uwasystemhealth/VM3000-Microphones/Images/16-GB-MicroSD.PNG

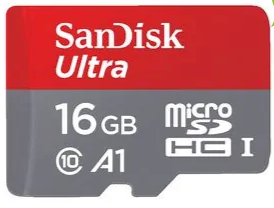
Images/16-GB-MicroSD.PNG
