uwasystemhealth/VM3000-Microphones/Images/05112020_PDM_Stereo.PNG

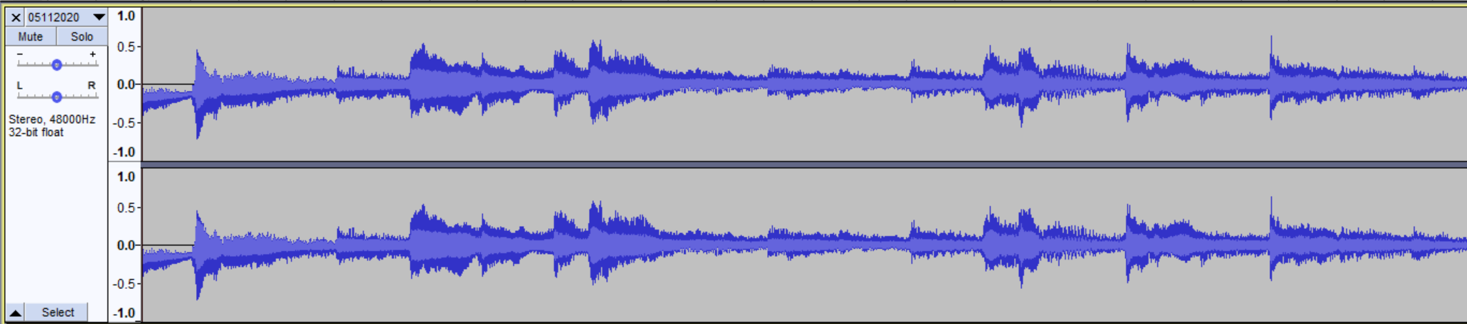
Images/05112020_PDM_Stereo.PNG
