uwasystemhealth/VM3000-Microphones/Images/I2S-MEMS-Breakout.jpg

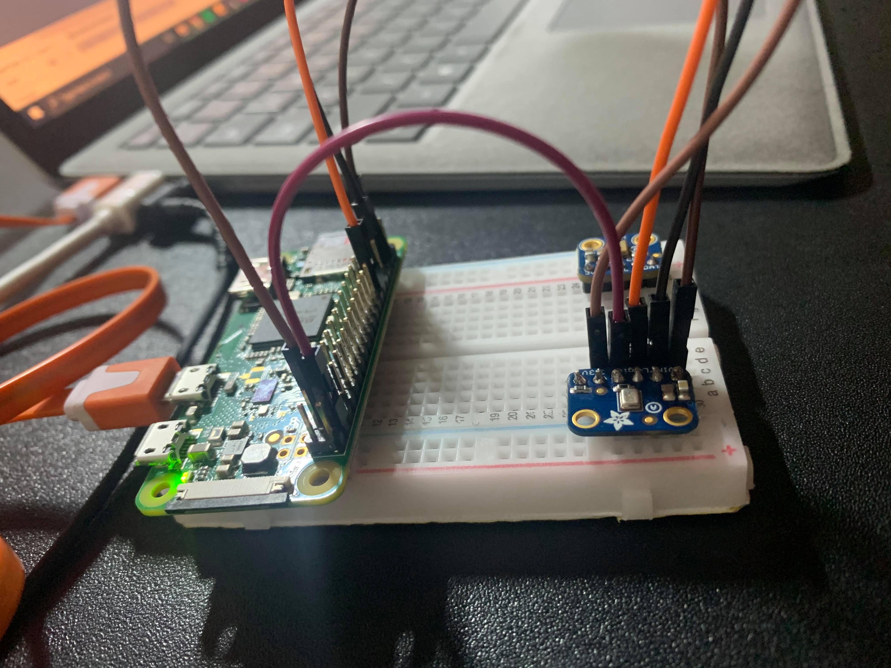
Images/I2S-MEMS-Breakout.jpg
