uwasystemhealth/VM3000-Microphones/Images/No_Phantom_Noise_Labelled_axes_legend_fixed.png

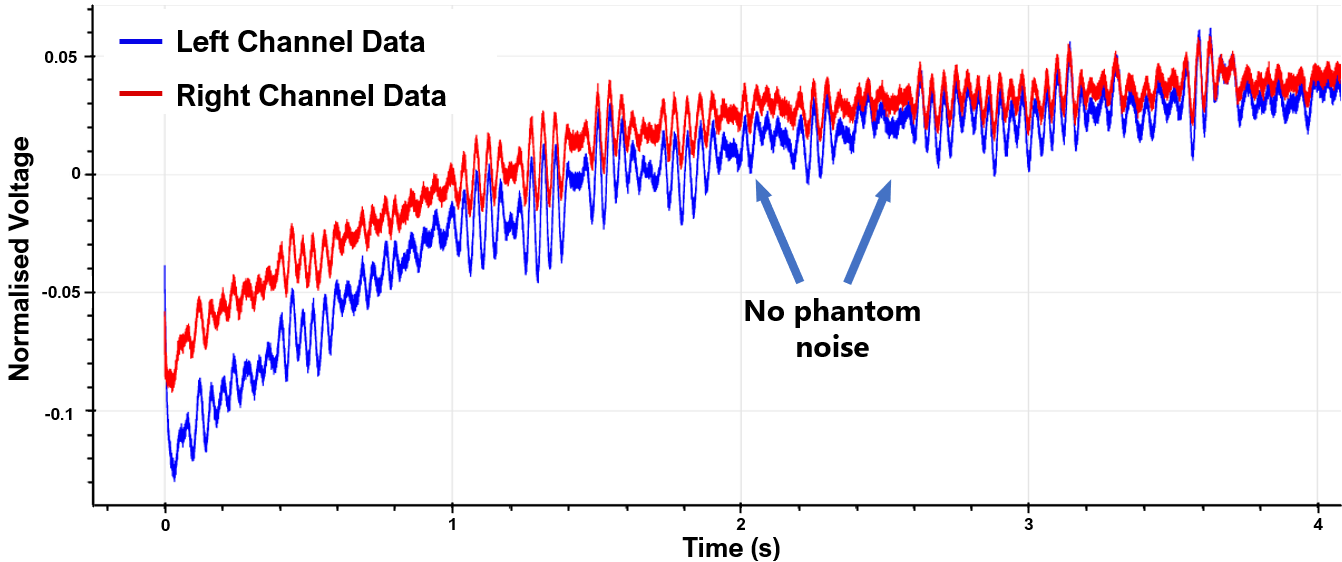
Images/No_Phantom_Noise_Labelled_axes_legend_fixed.png
