uwasystemhealth/VM3000-Microphones/Images/PDM-MEMS-Breakout.jpg

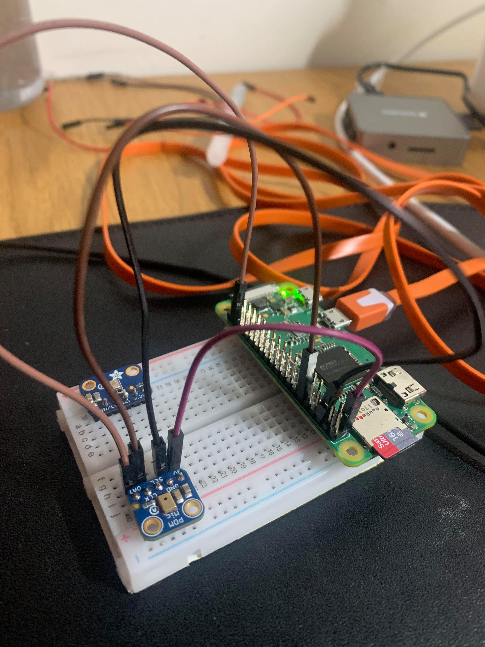
Images/PDM-MEMS-Breakout.jpg
