uwasystemhealth/VM3000-Microphones/Images/PDM_Microphone_Array_Prototype_Board.PNG

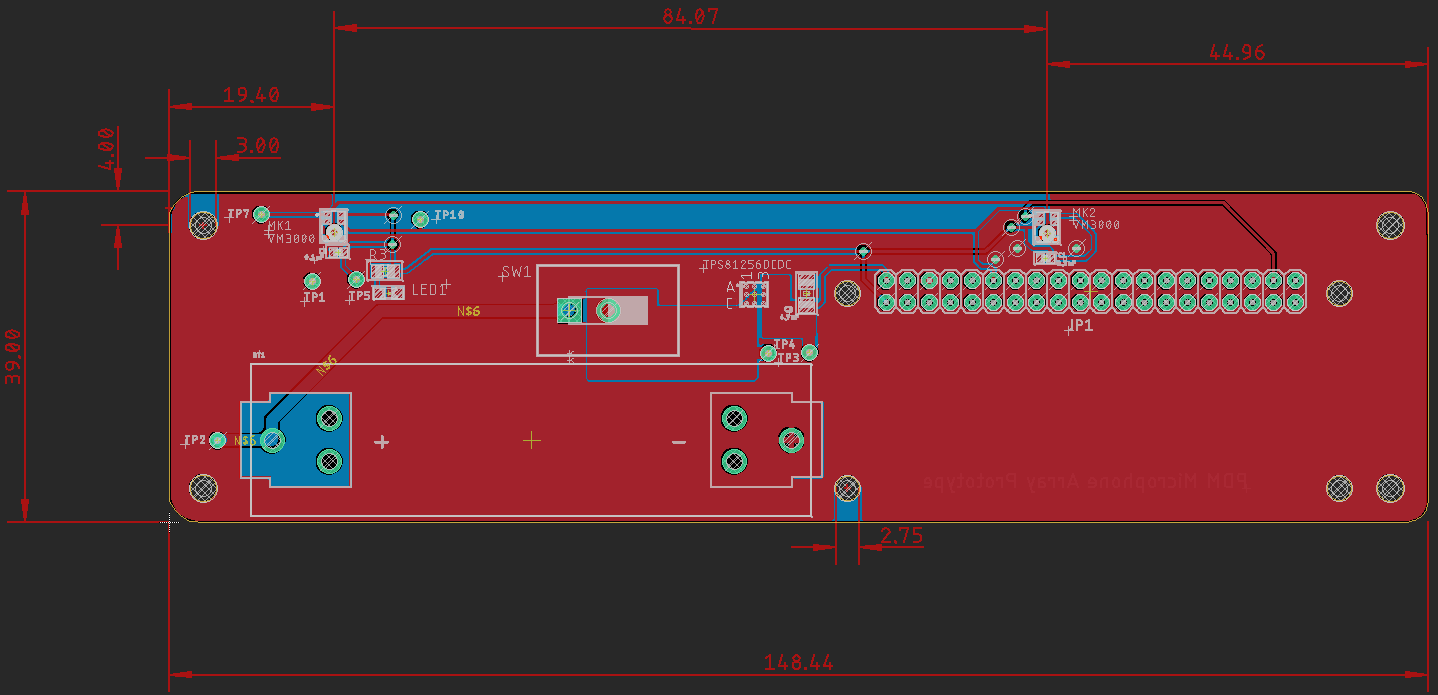
Images/PDM_Microphone_Array_Prototype_Board.PNG
