uwasystemhealth/VM3000-Microphones/Images/Phantom_Noise_1_labelled_axes_legend_fixed.png

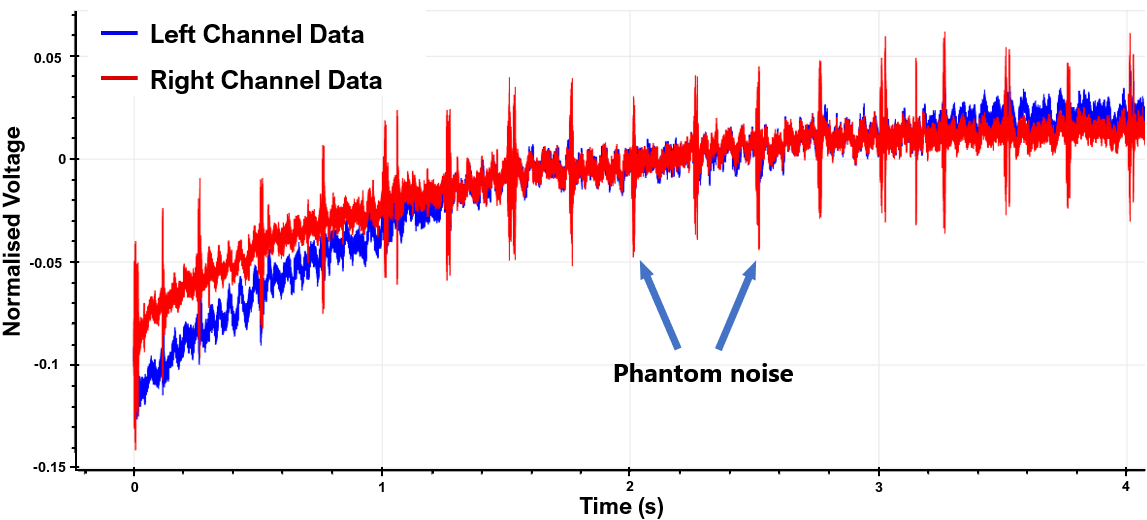
Images/Phantom_Noise_1_labelled_axes_legend_fixed.png
