uwasystemhealth/VM3000-Microphones/Images/Pi-Zero-W-GPIO.PNG

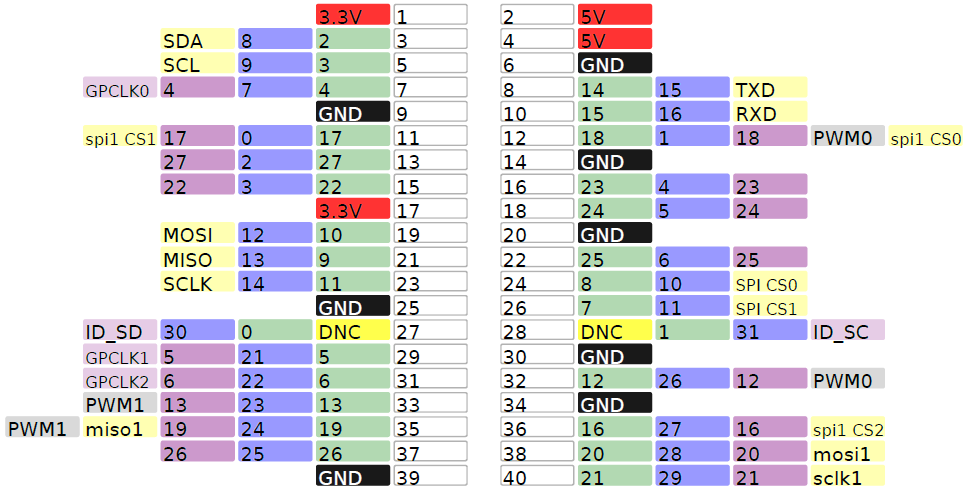
Images/Pi-Zero-W-GPIO.PNG
