uwasystemhealth/VM3000-Microphones/Images/Populated_Prototype_1.jpg

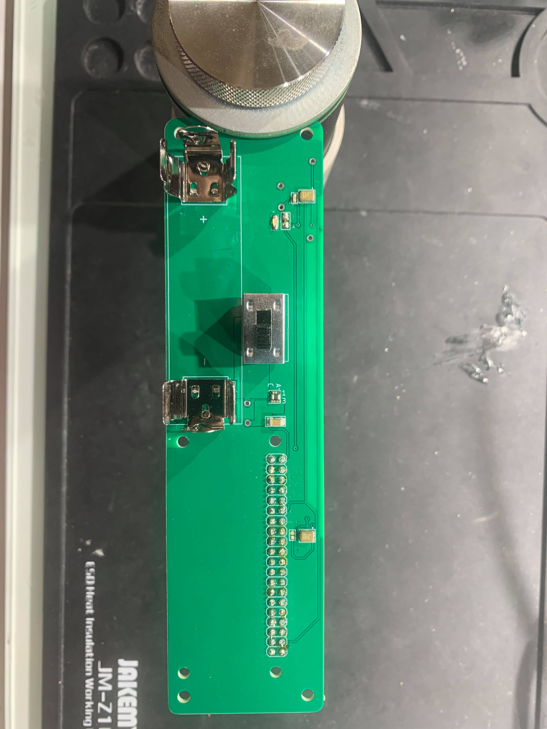
Images/Populated_Prototype_1.jpg
