uwasystemhealth/VM3000-Microphones/Images/Populated_Prototype_2.jpg

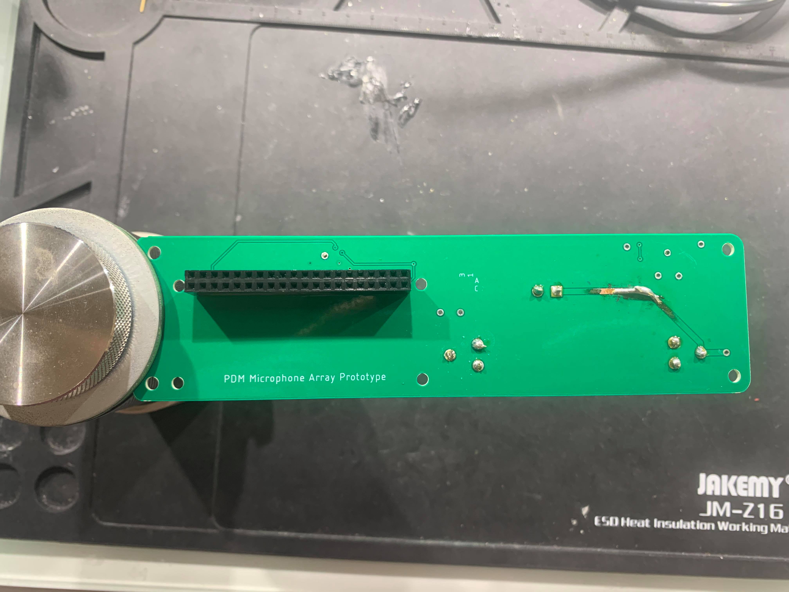
Images/Populated_Prototype_2.jpg
