uwasystemhealth/VM3000-Microphones/Images/Populated_Prototype_3.jpg

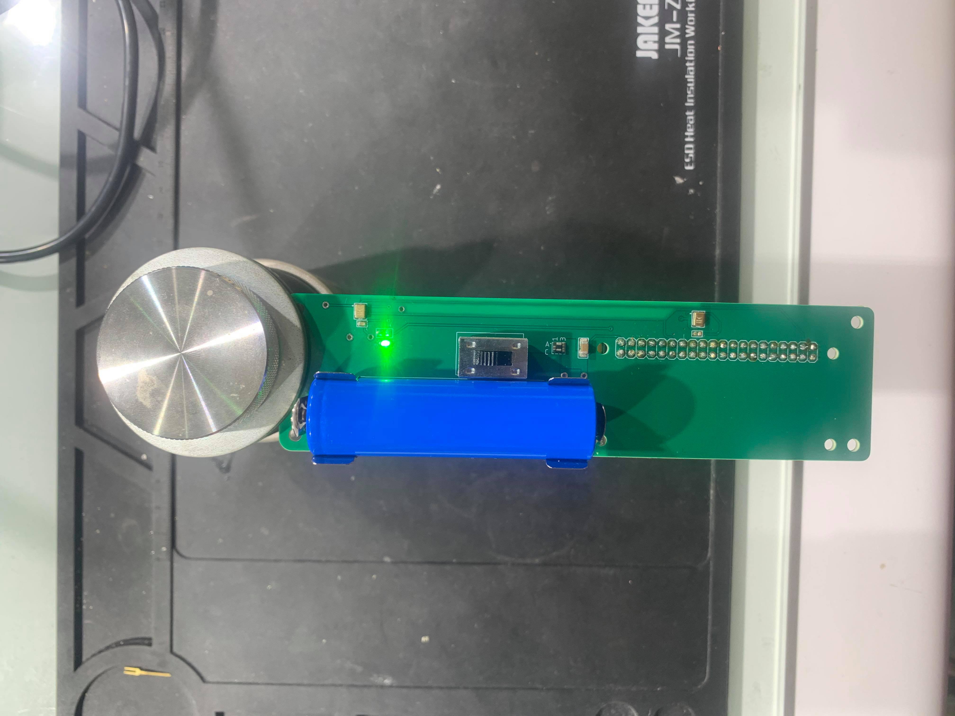
Images/Populated_Prototype_3.jpg
