uwasystemhealth/VM3000-Microphones/Images/Populated_Prototype_4.jpg

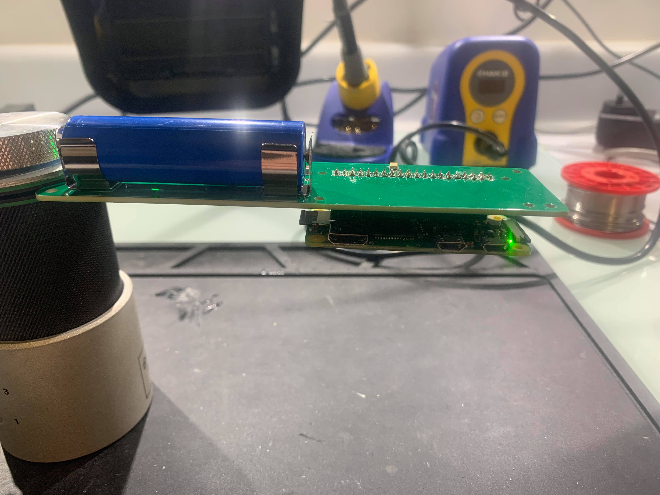
Images/Populated_Prototype_4.jpg
