uwasystemhealth/VM3000-Microphones/Images/Populated_Prototype_5.jpg

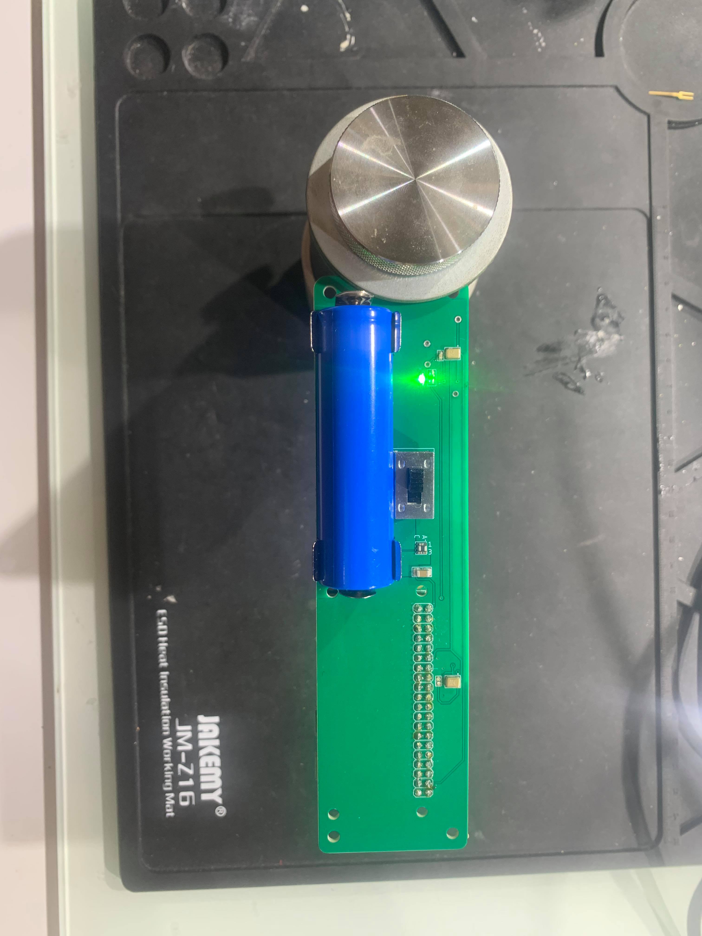
Images/Populated_Prototype_5.jpg
