uwasystemhealth/VM3000-Microphones/Images/Pulse-Density-Modulation-Example.png

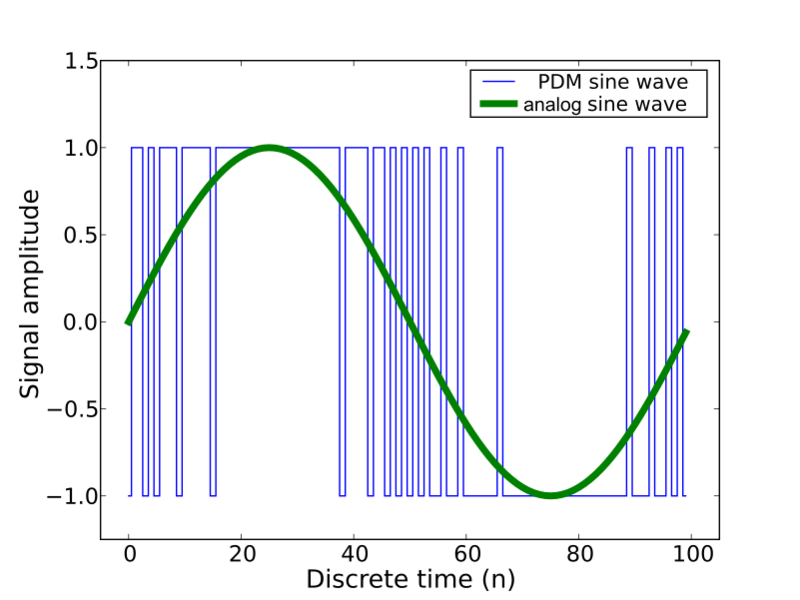
Images/Pulse-Density-Modulation-Example.png
