uwasystemhealth/VM3000-Microphones/Images/Sound-Circuit.jpg

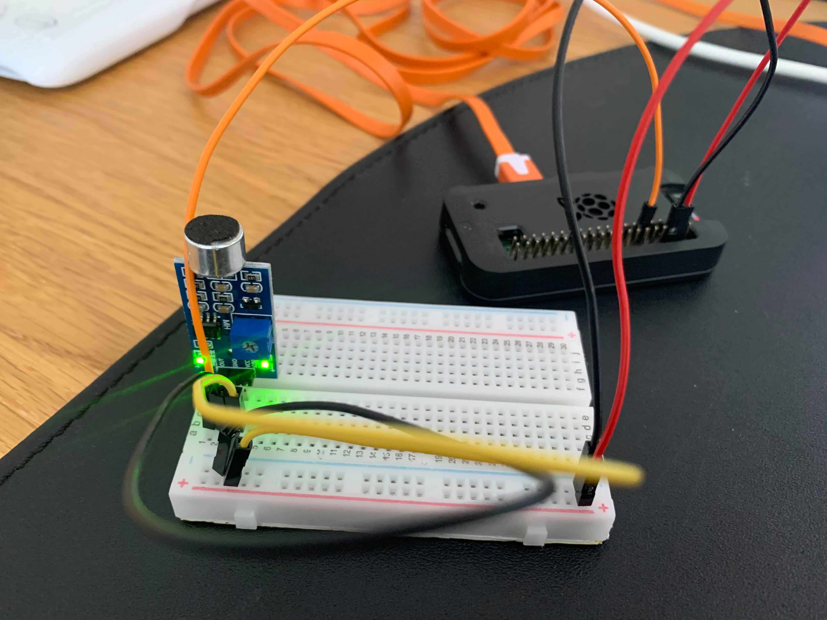
Images/Sound-Circuit.jpg
