uwasystemhealth/VM3000-Microphones/Images/Verbatim-Multi-Card-Reader.PNG

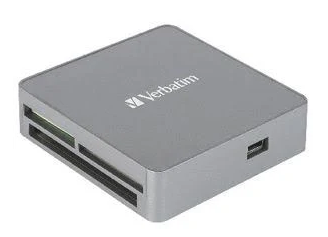
Images/Verbatim-Multi-Card-Reader.PNG
