uwasystemhealth/VM3000-Microphones/Images/WinSCP.PNG

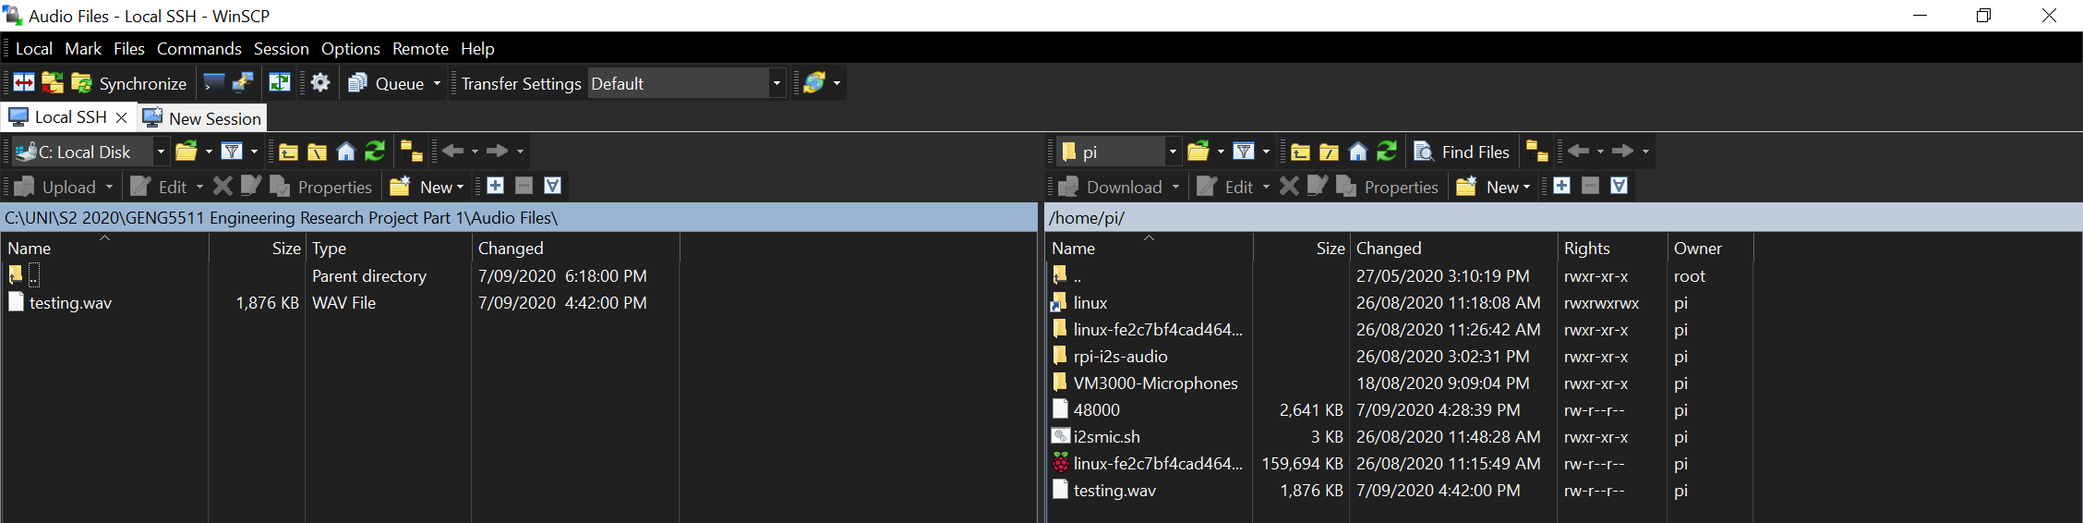
Images/WinSCP.PNG
