uwasystemhealth/VM3000-Microphones/Images/Anechoic_Setup_1.jpg

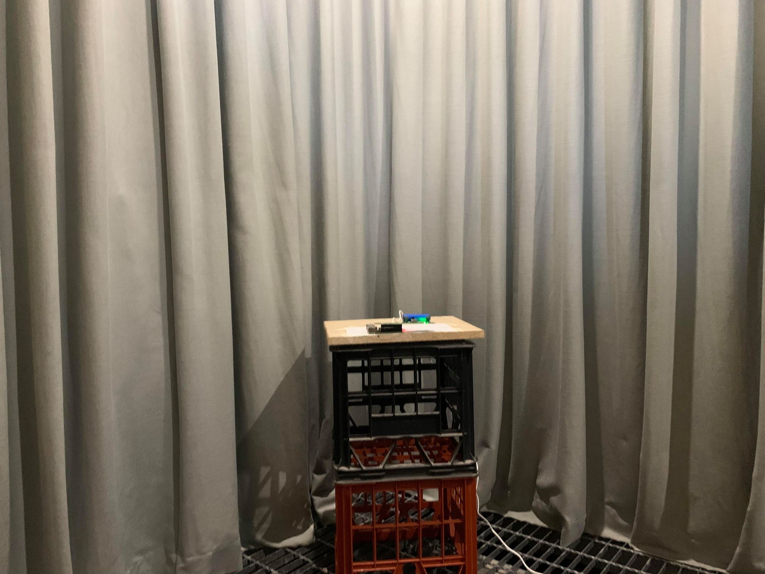
Images/Anechoic_Setup_1.jpg
