uwasystemhealth/VM3000-Microphones/Images/Setup_3.png

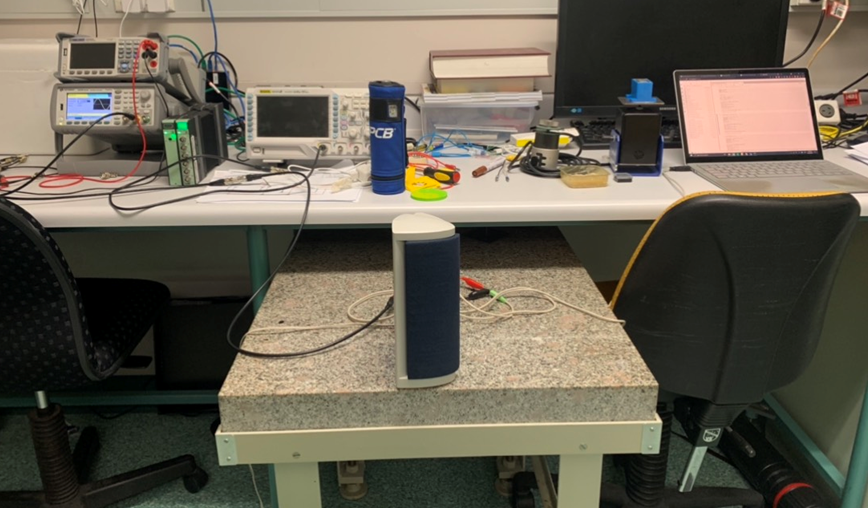
Images/Setup_3.png
