uwasystemhealth/VM3000-Microphones/Images/SHLSetup_1.png

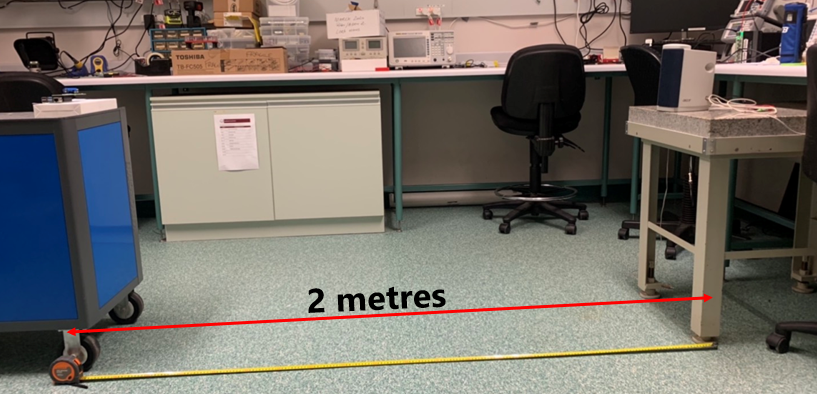
Images/SHLSetup_1.png
