uwasystemhealth/VM3000-Microphones/Images/SHLSetup_2.png

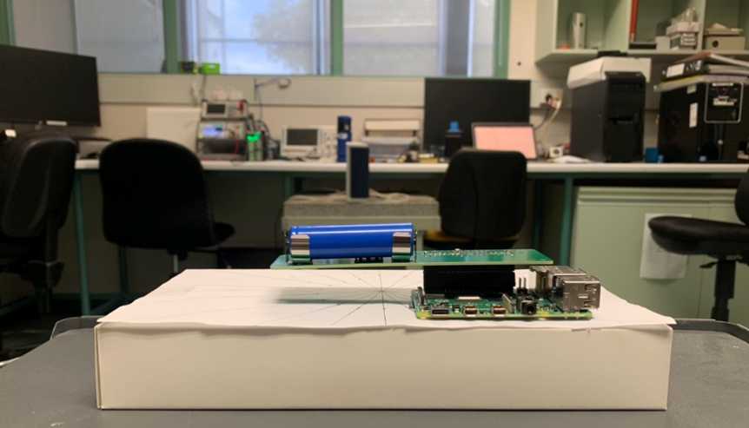
Images/SHLSetup_2.png
