uwasystemhealth/VM3000-Microphones/Images/PCM-Test-Waveform.PNG

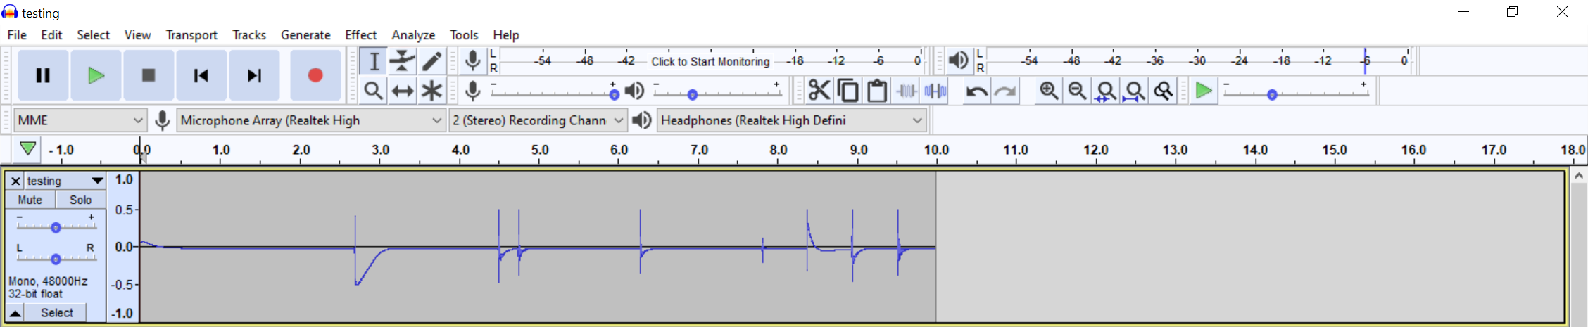
Images/PCM-Test-Waveform.PNG
