uwasystemhealth/VM3000-Microphones/Images/Sound-Circuit-Test.PNG

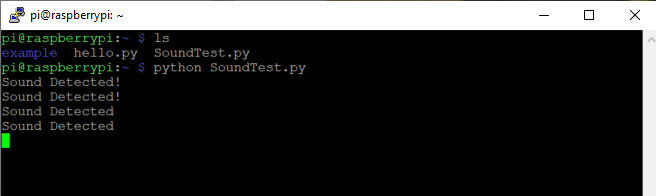
Images/Sound-Circuit-Test.PNG
